Ninjago77/apocalypse-beyond-sprout/images/20260709_095640.jpg

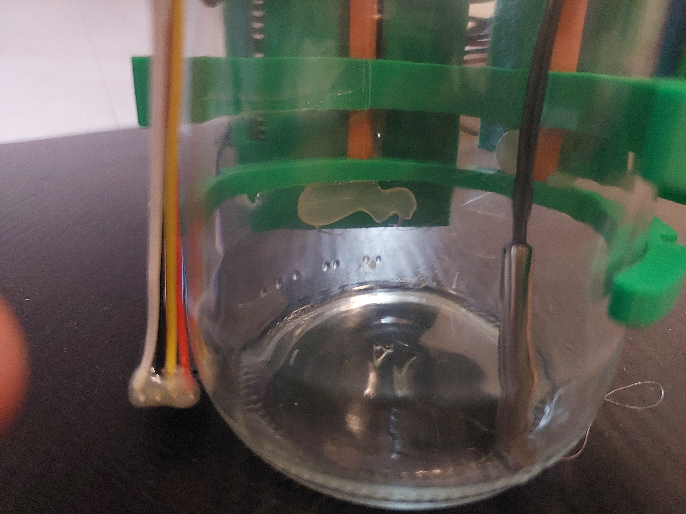
images/20260709_095640.jpg
