Ninjago77/apocalypse-beyond-sprout/images/20260709_095700.jpg

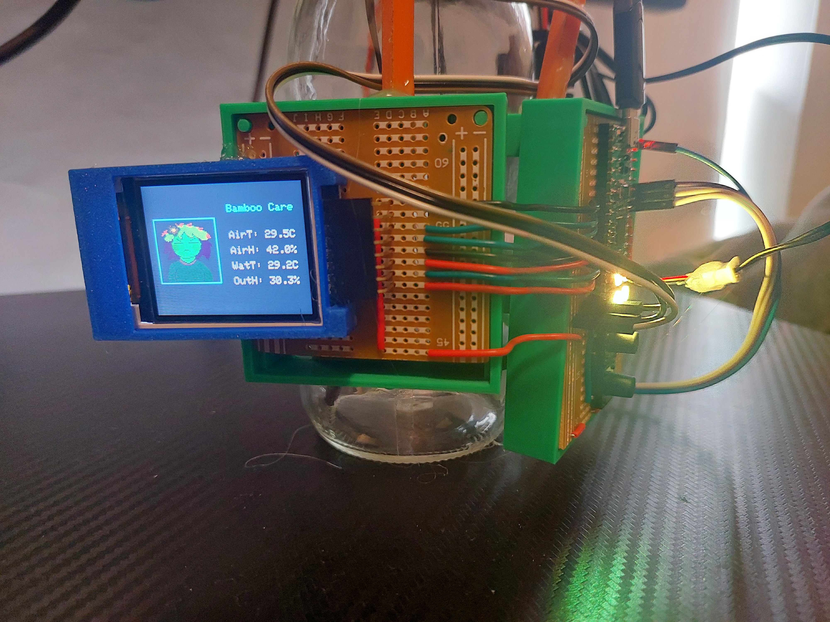
images/20260709_095700.jpg
