Ninjago77/apocalypse-beyond-sprout/images/20260709_095747.jpg

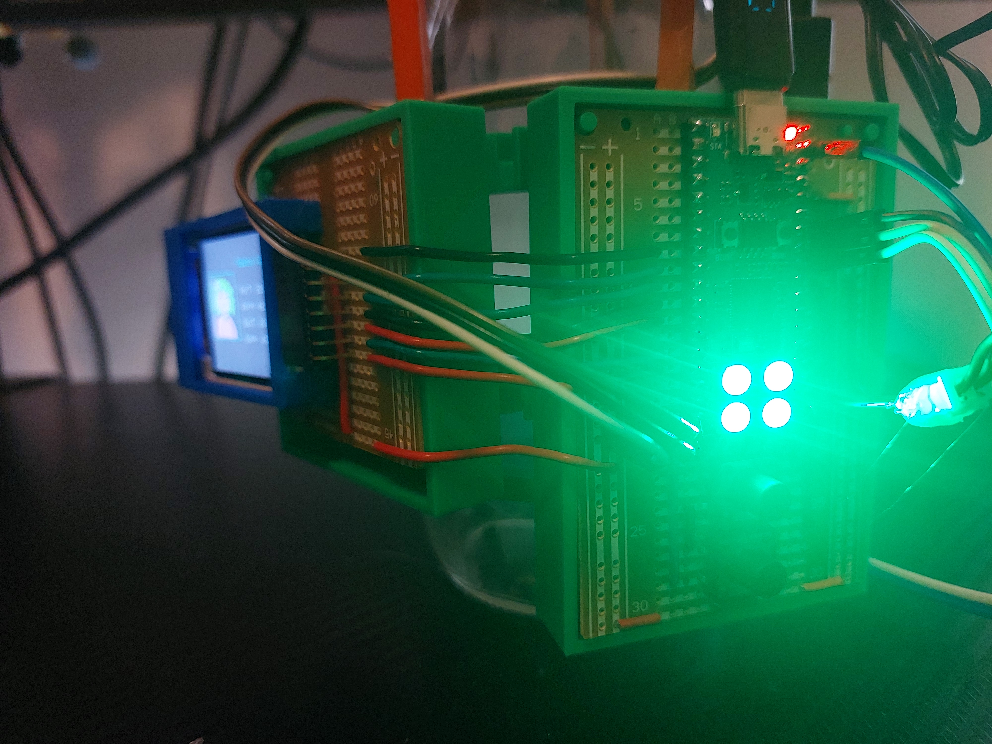
images/20260709_095747.jpg
