Ninjago77/apocalypse-beyond-sprout/images/WhatsApp Image 2026-07-03 at 22.15.47 (2).jpeg

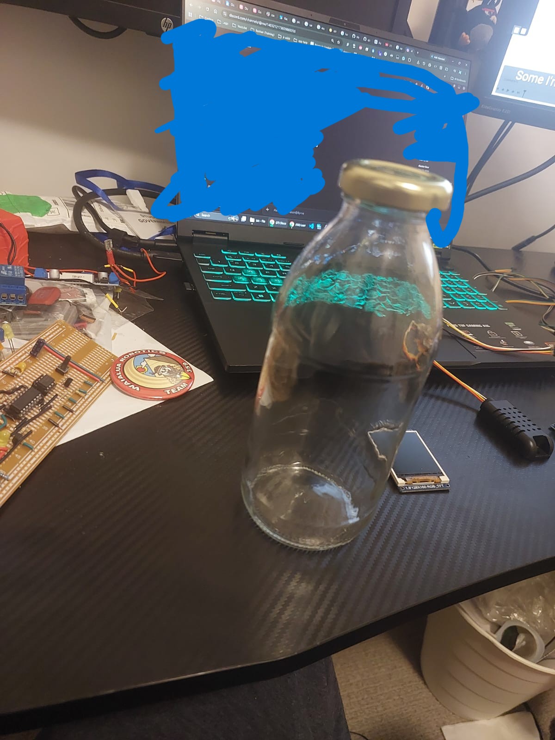
images/WhatsApp Image 2026-07-03 at 22.15.47 (2).jpeg
