Ninjago77/apocalypse-beyond-sprout/fusion_designs/split perf brackets 2 v3.step

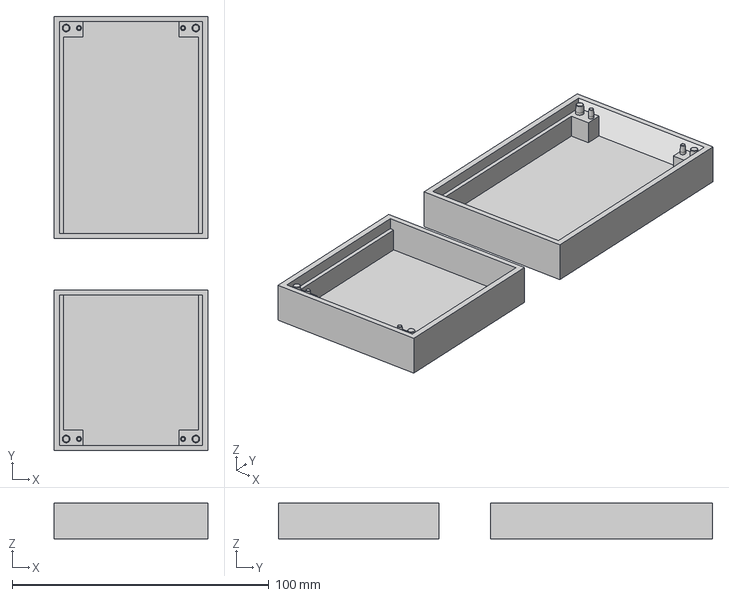
[picture p31: CAD file, 2026-07-09]
fusion_designs/split perf brackets 2 v3.step
60.0 x 169.1 x 14.0 mm
