Ninjago77/apocalypse-beyond-sprout/prints/test bottle bracket 4.3mf

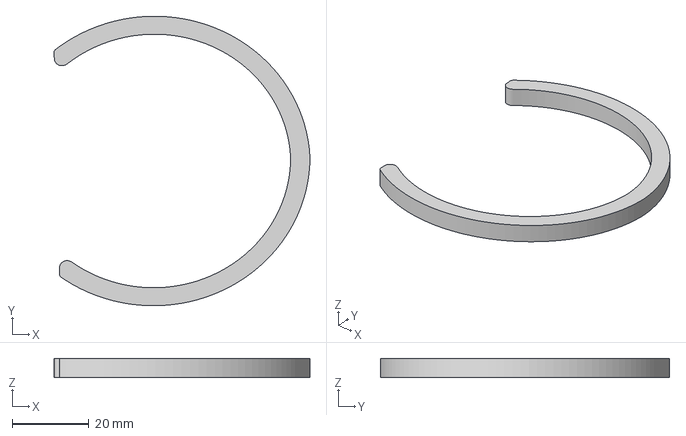
[picture p32: CAD file, 2026-07-09]
prints/test bottle bracket 4.3mf
66.6 x 75.3 x 5.00 mm
