Ninjago77/apocalypse-beyond-sprout/prints/test bottle bracket 2.3mf

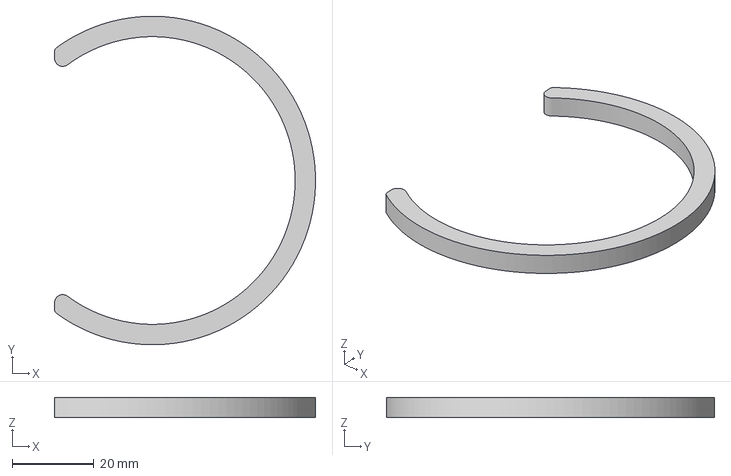
[picture p33: CAD file, 2026-07-09]
prints/test bottle bracket 2.3mf
64.0 x 80.5 x 5.00 mm
