Ninjago77/apocalypse-beyond-sprout/fusion_designs/split perf brackets v2.step

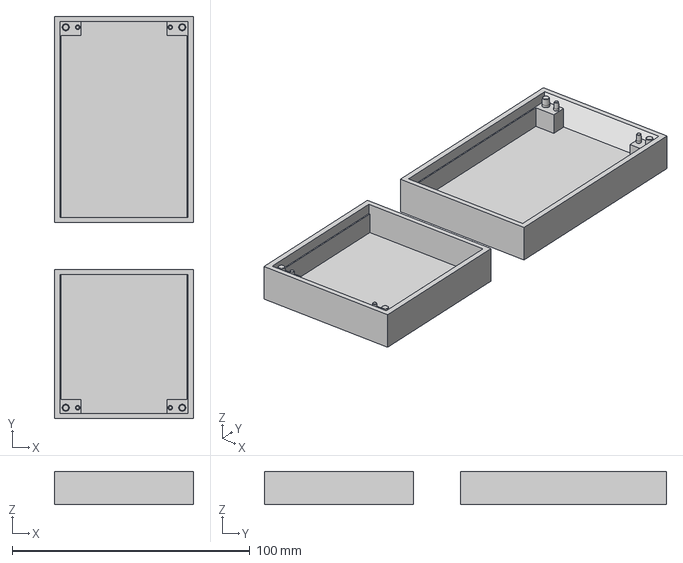
[picture p34: CAD file, 2026-07-09]
fusion_designs/split perf brackets v2.step
58.5 x 169.1 x 14.0 mm
