Ninjago77/apocalypse-beyond-sprout/prints/perfboard bracket test.3mf

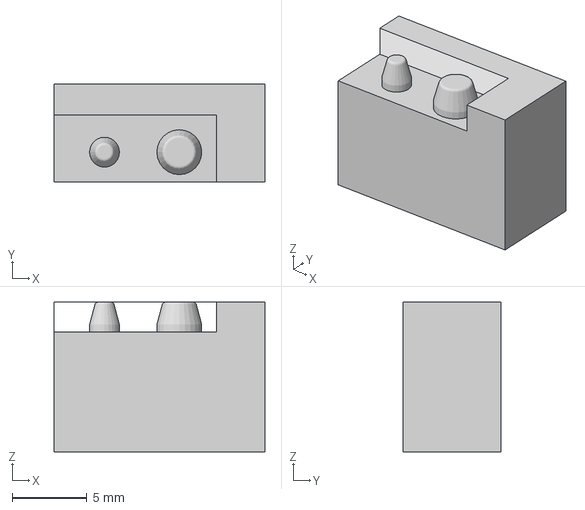
[picture p35: CAD file, 2026-07-09]
prints/perfboard bracket test.3mf
14.1 x 6.56 x 10.0 mm
