Ninjago77/apocalypse-beyond-sprout/fusion_designs/test bottle bracket v4.step

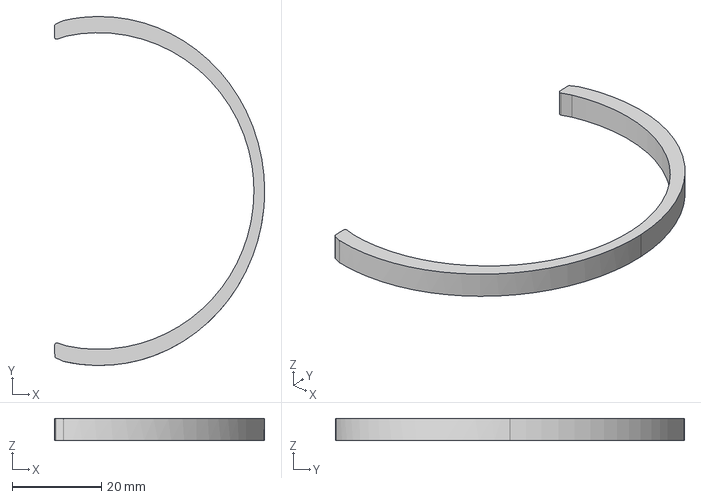
[picture p36: CAD file, 2026-07-09]
fusion_designs/test bottle bracket v4.step
47.1 x 78.1 x 5.00 mm
