Ninjago77/apocalypse-beyond-sprout/prints/display case.3mf

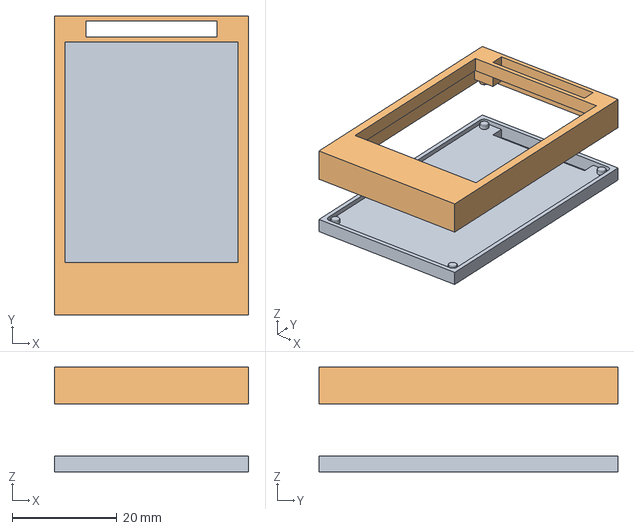
[picture p37: CAD file, 2026-07-09]
prints/display case.3mf
37.0 x 57.0 x 20.0 mm
