Ninjago77/apocalypse-beyond-sprout/fusion_designs/display v3-dup.step

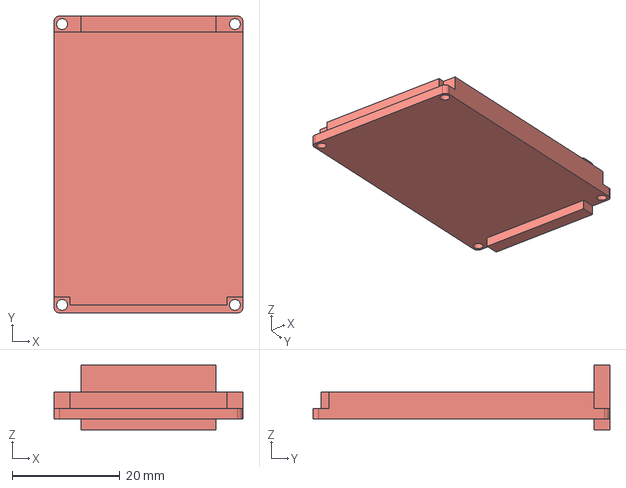
[picture p38: CAD file, 2026-07-09]
fusion_designs/display v3-dup.step
35.0 x 55.0 x 12.0 mm
