Ninjago77/apocalypse-beyond-sprout/fusion_designs/bottle region v6.step

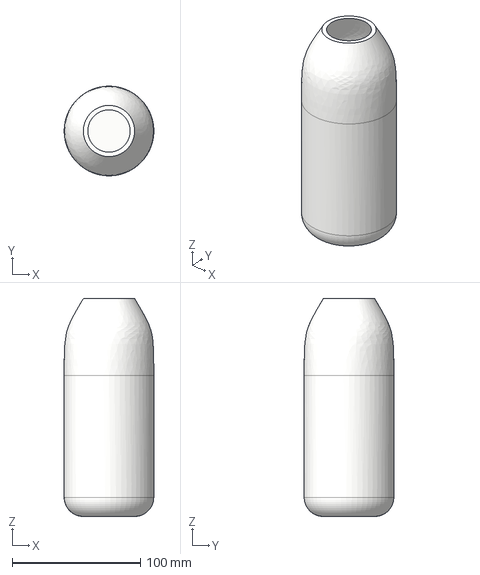
[picture p39: CAD file, 2026-07-09]
fusion_designs/bottle region v6.step
70.0 x 70.0 x 170.0 mm
