Ninjago77/apocalypse-beyond-sprout/fusion_designs/perfboard bracket test v2.step

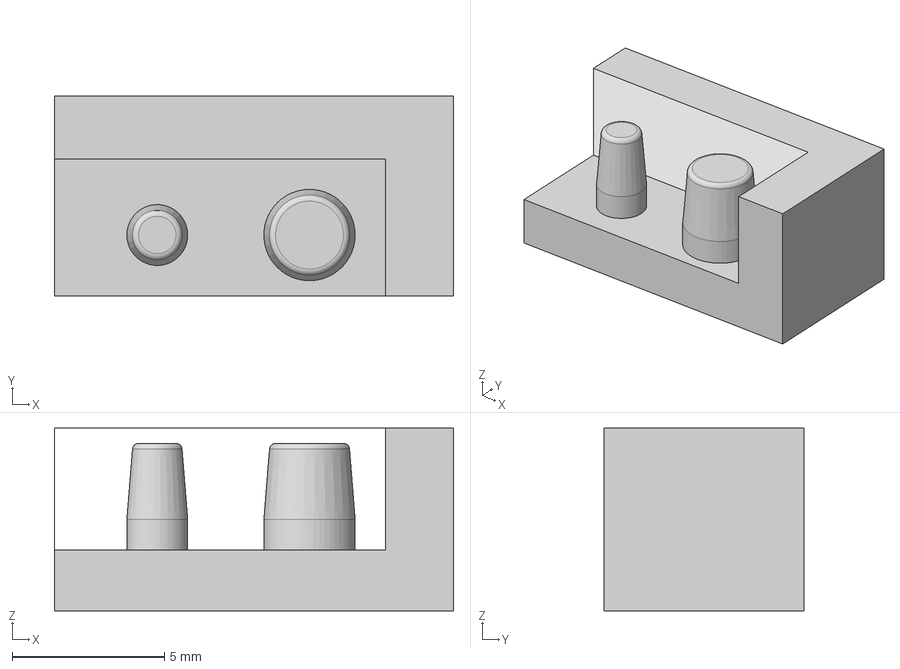
[picture p40: CAD file, 2026-07-09]
fusion_designs/perfboard bracket test v2.step
13.1 x 6.56 x 6.00 mm
