Ninjago77/apocalypse-beyond-sprout/images/20260706_140346.jpg

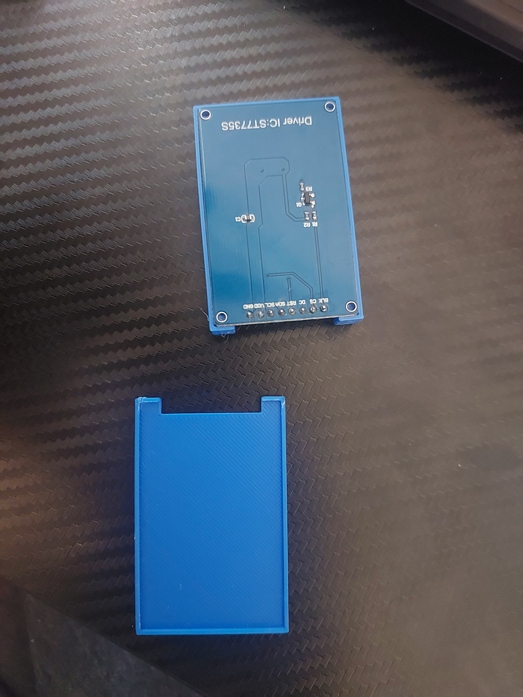
images/20260706_140346.jpg
