Ninjago77/apocalypse-beyond-sprout/images/20260709_095628.jpg

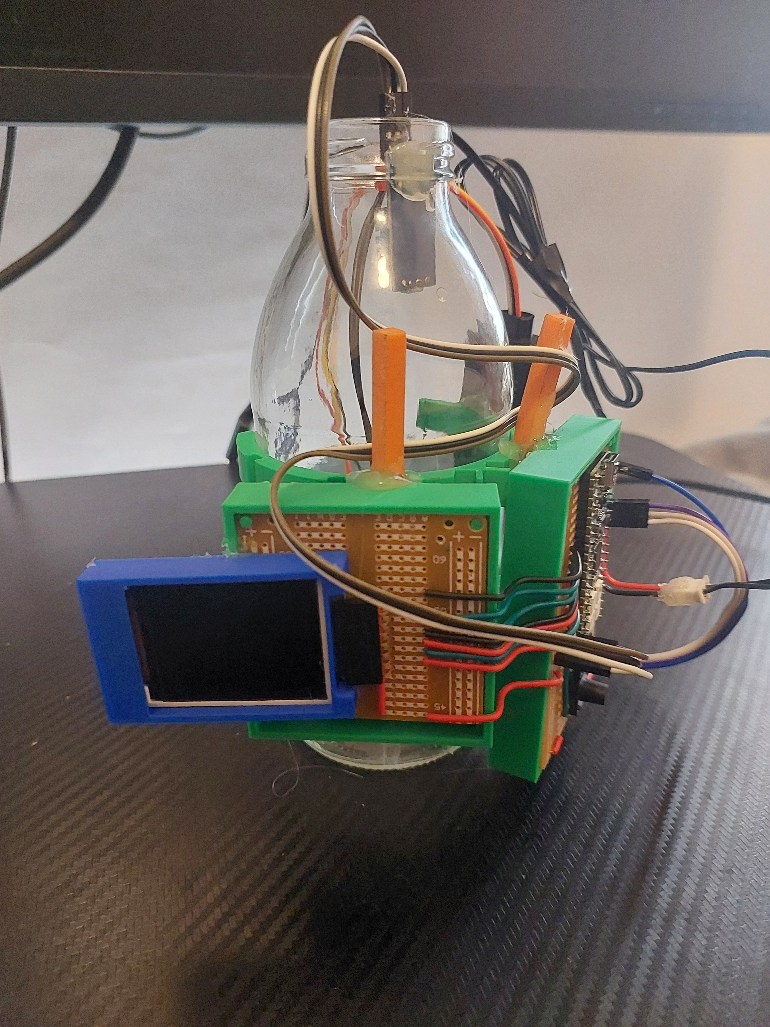
images/20260709_095628.jpg
