Ninjago77/apocalypse-beyond-sprout/images/20260709_101424.jpg

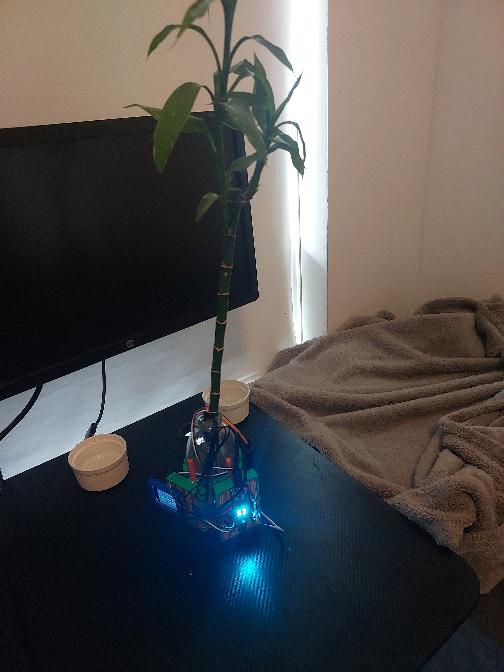
images/20260709_101424.jpg
