Ninjago77/apocalypse-beyond-sprout/images/20260709_101458.jpg

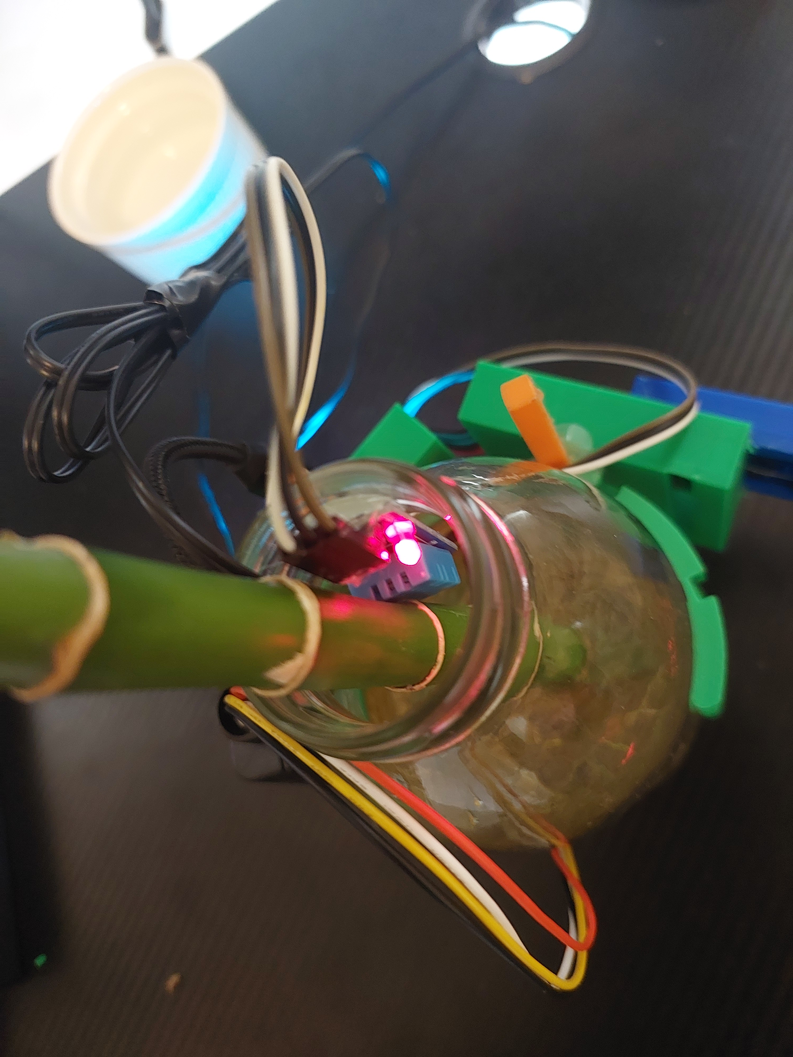
images/20260709_101458.jpg
