Ninjago77/apocalypse-beyond-sprout/images/20260709_101506.jpg

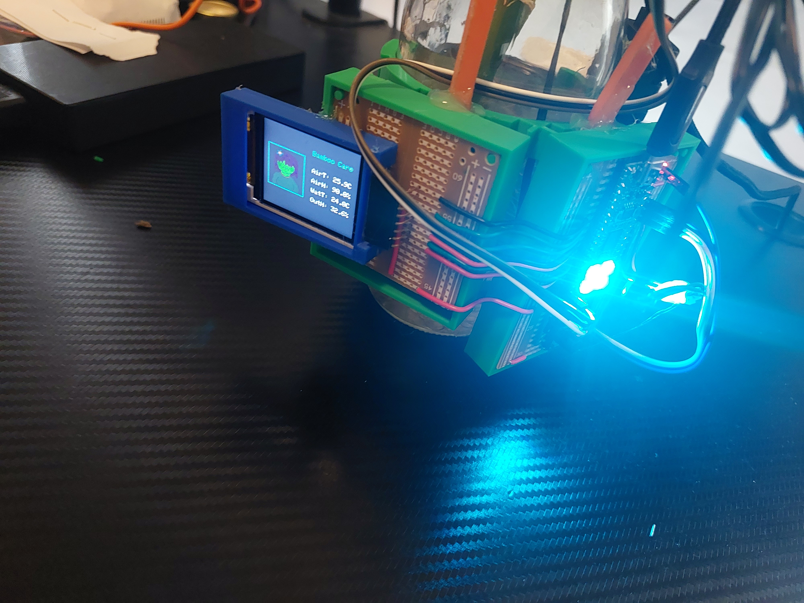
images/20260709_101506.jpg
